BlackElkX/GhotiTnTdevices/src/Global.hpp

#include <ESP8266WiFi.h>
#include <ESP8266WebServer.h>
#include <Arduino.h>
#include <WString.h>

bool getDebugPinState();
void debugToSerial(const String message);
void debugLineToSerial(const String message);
void debugToSerial(const int message);
void debugLineToSerial(const int message);
