BlackElkX/GhotiTnTdevices/src/Global.cpp

#include <Arduino.h>
#include <WString.h>
#include "PersistentSettings.hpp"

extern DebugStruct debugInfo;

bool getDebugPinState() {
  return !(digitalRead(debugInfo.pin) > 0);
}

void debugToSerial(const String message) {
  if (getDebug() || getDebugPinState()) {
    Serial.print(message);
  }
}

void debugLineToSerial(const String message) {
  if (getDebug() || getDebugPinState()) {
    Serial.println(message);
  }
}

void debugToSerial(const int message) {
  debugToSerial(String(message));
}

void debugLineToSerial(const int message) {
  debugLineToSerial(String(message));
}
